SanPollo/PCWBackplane/schematics/PCWBackplaneV1.1.kicad_sch

## KiCad design schematics/PCWBackplaneV1.1.kicad_sch (2025-11-17)

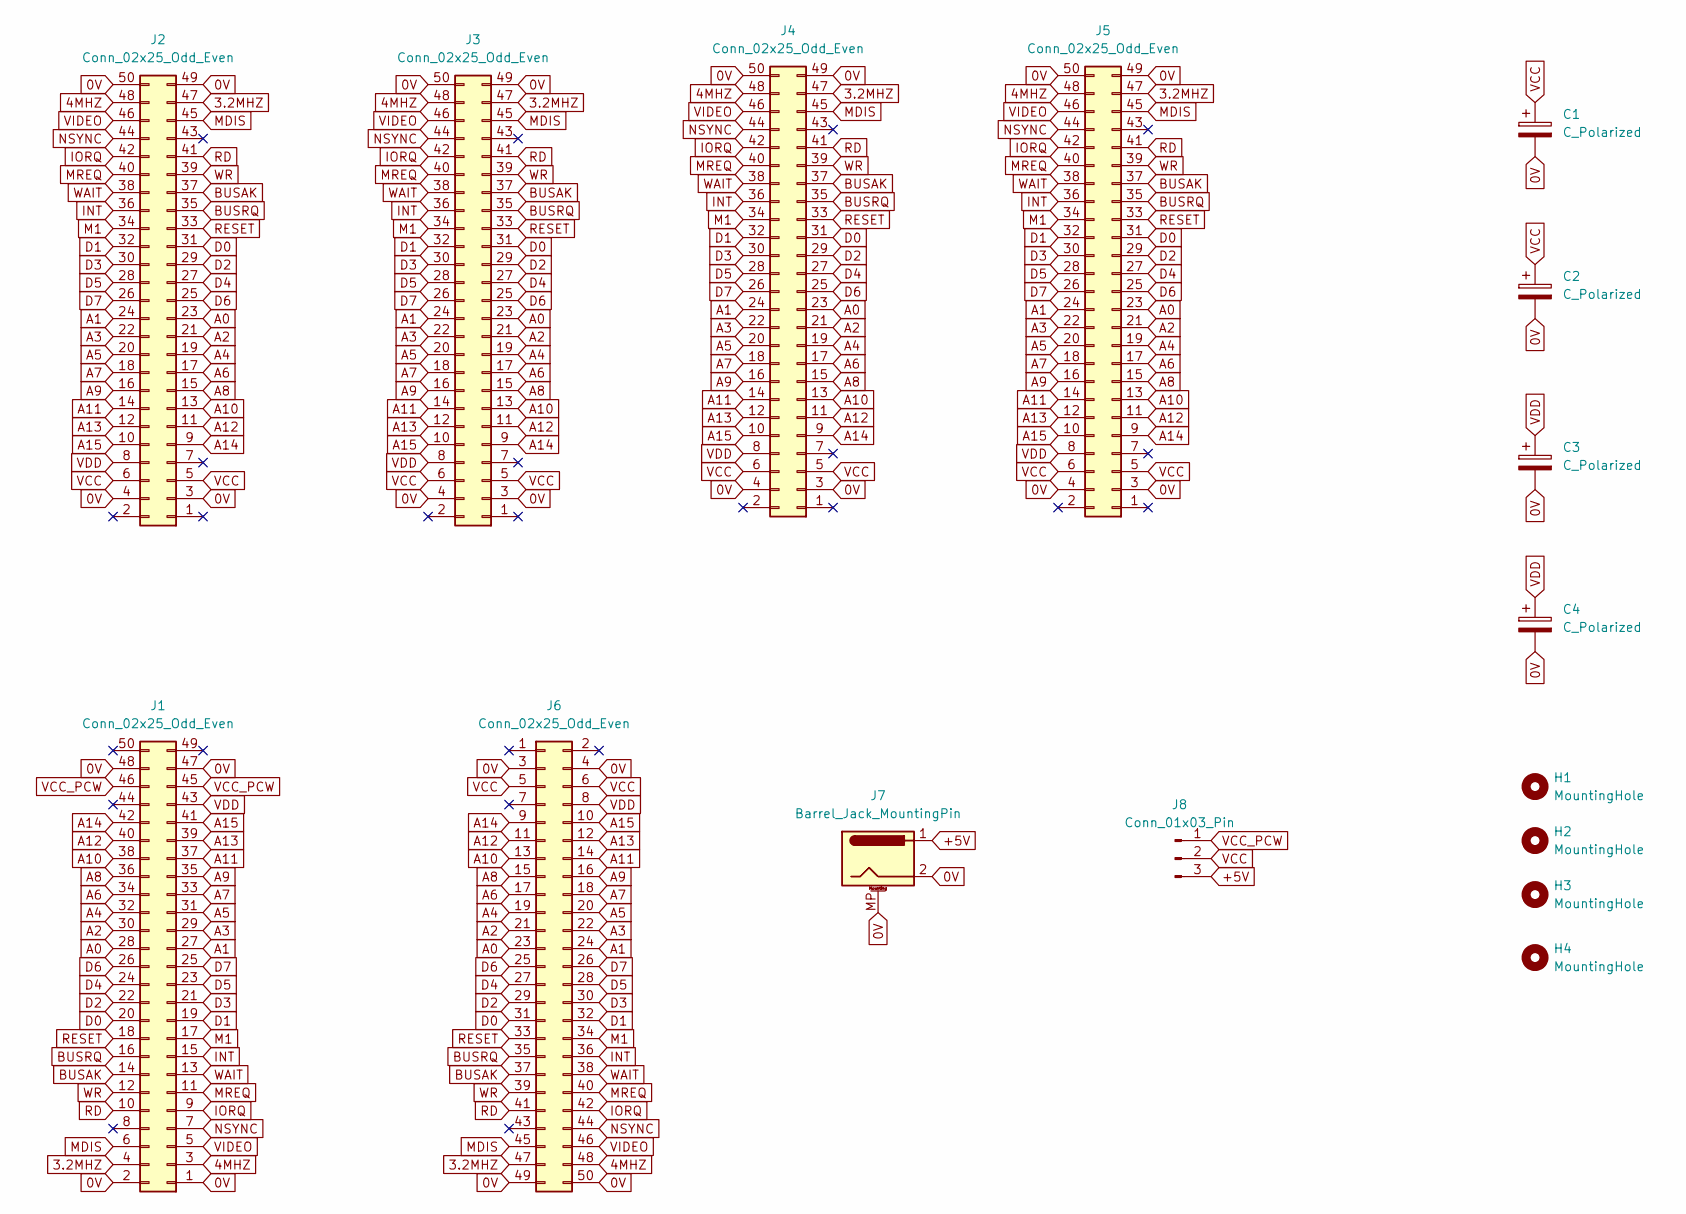
[picture p6: schematic PCWBackplaneV1.1.kicad_sch]

Parts:
C1, C2, C3, C4: C_Polarized; CP_Radial_D5.0mm_P2.50mm
H1, H2, H3, H4: MountingHole; MountingHole_2.7mm_M2.5_ISO7380
J1, J6: Conn_02x25_Odd_Even; IDC-Header_2x25_P2.54mm_Horizontal
J2, J3, J4, J5: Conn_02x25_Odd_Even; PinSocket_2x25_P2.54mm_Vertical_Keyed
J7: Barrel_Jack_MountingPin; BarrelJack_Horizontal
J8: Conn_01x03_Pin; PinHeader_1x03_P2.54mm_Vertical

Connections:
0V: C1.2, C2.2, C3.2, C4.2, J1.1, J1.2, J1.47, J1.48, J2.3, J2.4, J2.49, J2.50, J3.3, J3.4, J3.49, J3.50, J4.3, J4.4, J4.49, J4.50, J5.3, J5.4, J5.49, J5.50, J6.3, J6.4, J6.49, J6.50, J7.2, J7.MP (MountPin)
3.2MHZ: J1.4, J2.47, J3.47, J4.47, J5.47, J6.47
4MHZ: J1.3, J2.48, J3.48, J4.48, J5.48, J6.48
+5V: J7.1, J8.3
A0: J1.28, J2.23, J3.23, J4.23, J5.23, J6.23
A1: J1.27, J2.24, J3.24, J4.24, J5.24, J6.24
A2: J1.30, J2.21, J3.21, J4.21, J5.21, J6.21
A3: J1.29, J2.22, J3.22, J4.22, J5.22, J6.22
A4: J1.32, J2.19, J3.19, J4.19, J5.19, J6.19
A5: J1.31, J2.20, J3.20, J4.20, J5.20, J6.20
A6: J1.34, J2.17, J3.17, J4.17, J5.17, J6.17
A7: J1.33, J2.18, J3.18, J4.18, J5.18, J6.18
A8: J1.36, J2.15, J3.15, J4.15, J5.15, J6.15
A9: J1.35, J2.16, J3.16, J4.16, J5.16, J6.16
A10: J1.38, J2.13, J3.13, J4.13, J5.13, J6.13
A11: J1.37, J2.14, J3.14, J4.14, J5.14, J6.14
A12: J1.40, J2.11, J3.11, J4.11, J5.11, J6.11
A13: J1.39, J2.12, J3.12, J4.12, J5.12, J6.12
A14: J1.42, J2.9, J3.9, J4.9, J5.9, J6.9
A15: J1.41, J2.10, J3.10, J4.10, J5.10, J6.10
BUSAK: J1.14, J2.37, J3.37, J4.37, J5.37, J6.37
BUSRQ: J1.16, J2.35, J3.35, J4.35, J5.35, J6.35
D0: J1.20, J2.31, J3.31, J4.31, J5.31, J6.31
D1: J1.19, J2.32, J3.32, J4.32, J5.32, J6.32
D2: J1.22, J2.29, J3.29, J4.29, J5.29, J6.29
D3: J1.21, J2.30, J3.30, J4.30, J5.30, J6.30
D4: J1.24, J2.27, J3.27, J4.27, J5.27, J6.27
D5: J1.23, J2.28, J3.28, J4.28, J5.28, J6.28
D6: J1.26, J2.25, J3.25, J4.25, J5.25, J6.25
D7: J1.25, J2.26, J3.26, J4.26, J5.26, J6.26
INT: J1.15, J2.36, J3.36, J4.36, J5.36, J6.36
IORQ: J1.9, J2.42, J3.42, J4.42, J5.42, J6.42
M1: J1.17, J2.34, J3.34, J4.34, J5.34, J6.34
MDIS: J1.6, J2.45, J3.45, J4.45, J5.45, J6.45
MREQ: J1.11, J2.40, J3.40, J4.40, J5.40, J6.40
NSYNC: J1.7, J2.44, J3.44, J4.44, J5.44, J6.44
RD: J1.10, J2.41, J3.41, J4.41, J5.41, J6.41
RESET: J1.18, J2.33, J3.33, J4.33, J5.33, J6.33
VCC: C1.1, C2.1, J2.5, J2.6, J3.5, J3.6, J4.5, J4.6, J5.5, J5.6, J6.5, J6.6, J8.2
VCC_PCW: J1.45, J1.46, J8.1
VDD: C3.1, C4.1, J1.43, J2.8, J3.8, J4.8, J5.8, J6.8
VIDEO: J1.5, J2.46, J3.46, J4.46, J5.46, J6.46
WAIT: J1.13, J2.38, J3.38, J4.38, J5.38, J6.38
WR: J1.12, J2.39, J3.39, J4.39, J5.39, J6.39
